Anindita-SA/Quadrature-Oscillator---Sine-Cosine-Waveform-Generator/LTSpice simulation for 1kHz SineCosine Generator/1kHz sinecosine gen.asc

C1: cap; 100n
C2: cap; 100n
C3: cap; 100n
C4: cap; 0.1µ
C5: cap; 0.1µ
D1: diode; 1N4148
D2: diode; 1N4148
R1: res; 1.6k
R2: res; 1.6k
R3: res; 1.6k
R4: res; 1.6k
R5: res; 1k
R6: res; 8k
R7: res; 1k
R8: res; 10k
R9: res; 10k
R10: res; 8k
U1: LM358
U2: LM358
V1: voltage; 30
Named nets: V2, V1, 0, Sine_out, Cosine_out
.tran 500m
.ic V(Cosine_out)=1
